leon-red/St1x/Software/Core/Inc/main.h

#define INT1_Pin GPIO_PIN_0
#define INT1_GPIO_Port GPIOA
#define INT1_EXTI_IRQn EXTI0_IRQn
#define TEMP_CON1_Pin GPIO_PIN_1
#define TEMP_CON1_GPIO_Port GPIOA
#define USB_VOLT_DET_Pin GPIO_PIN_2
#define USB_VOLT_DET_GPIO_Port GPIOA
#define KEY_DOWN_Pin GPIO_PIN_5
#define KEY_DOWN_GPIO_Port GPIOA
#define KEY_DOWN_EXTI_IRQn EXTI9_5_IRQn
#define KEY_MODE_Pin GPIO_PIN_6
#define KEY_MODE_GPIO_Port GPIOA
#define KEY_MODE_EXTI_IRQn EXTI9_5_IRQn
#define KEY_UP_Pin GPIO_PIN_7
#define KEY_UP_GPIO_Port GPIOA
#define KEY_UP_EXTI_IRQn EXTI9_5_IRQn
#define Buzzer_Pin GPIO_PIN_0
#define Buzzer_GPIO_Port GPIOB
#define OLED_IM_Pin GPIO_PIN_10
#define OLED_IM_GPIO_Port GPIOB
#define G_CS_Pin GPIO_PIN_11
#define G_CS_GPIO_Port GPIOB
#define OLED_CS_Pin GPIO_PIN_12
#define OLED_CS_GPIO_Port GPIOB
#define SPI2_SCK_Pin GPIO_PIN_13
#define SPI2_SCK_GPIO_Port GPIOB
#define SPI2_MISO_Pin GPIO_PIN_14
#define SPI2_MISO_GPIO_Port GPIOB
#define SPI2_MOSI_Pin GPIO_PIN_15
#define SPI2_MOSI_GPIO_Port GPIOB
#define OLED_DC_Pin GPIO_PIN_8
#define OLED_DC_GPIO_Port GPIOA
#define OLED_PW_EN_Pin GPIO_PIN_15
#define OLED_PW_EN_GPIO_Port GPIOA
#define OLED_Reset_Pin GPIO_PIN_3
#define OLED_Reset_GPIO_Port GPIOB
#define LED_BLUE_Pin GPIO_PIN_4
#define LED_BLUE_GPIO_Port GPIOB
#define LED_RGB_Pin GPIO_PIN_5
#define LED_RGB_GPIO_Port GPIOB
#define LED_GREEN_Pin GPIO_PIN_8
#define LED_GREEN_GPIO_Port GPIOB
#define LED_RED_Pin GPIO_PIN_9
#define LED_RED_GPIO_Port GPIOB
