leon-red/St1x/Software/St1xDrivers/St1xStatic.c

#include "St1xStatic.h"
#include "lis2dw12_reg.h"
#include "main.h"
#include "spi.h"
#include "St1xADC.h"
#include "St1xKey.h"
#include "St1xPID.h"
#include "St1xFlash.h"
#include "u8g2.h"
#include <stdio.h>
#include <string.h>
#include <math.h>

// 传感器相关变量
static stmdev_ctx_t dev_ctx;
static int16_t data_raw_acceleration[3];
static float acceleration_mg[3];
static uint8_t whoamI;
static uint8_t sensor_initialized = 0;
static float last_acceleration_mg[3] = {0.0f, 0.0f, 0.0f};  // 用于静置检测的上一帧数据
static float acceleration_change[3] = {0.0f, 0.0f, 0.0f};
static float zero_calibration_offset[3] = {0.0f, 0.0f, 0.0f};  // 归零校准的基准值
static uint8_t zero_calibration_saved = 0;  // 标记是否已保存归零校准数据到FLASH

// 静置时间控制参数（可配置，单位：分钟）
#define DEFAULT_STANDBY_TIME_REDUCE_TEMP 15    // 15分钟后进入休眠状态
#define DEFAULT_STANDBY_TIME_TURN_OFF 30       // 30分钟停止加热
#define DEFAULT_REDUCED_TEMPERATURE 160.0f    // 休眠状态下的温度维持

// 时间单位转换宏
#define MINUTES_TO_MILLISECONDS(minutes) ((minutes) * 60 * 1000)

// 静置时间控制变量
static uint32_t last_movement_time = 0;
static uint32_t standby_start_time = 0;
static uint8_t is_in_standby_mode = 0;
static uint8_t is_in_sleep_mode = 0;
static float original_target_temperature = 0.0f;
static uint8_t standby_mode_initialized = 0;
static uint8_t manually_stopped = 0;

// OLED屏幕亮度控制相关变量
static uint8_t oled_brightness = 255;
static uint8_t oled_standby_brightness = 76;
static u8g2_t* global_u8g2 = NULL;

// 传感器误差阈值，用于过滤小幅度的数值跳变
#define MOVEMENT_THRESHOLD 50.0f                      // 运动检测阈值 (mg)
#define STANDBY_TIME_THRESHOLD 5000                   // 静置时间阈值 (ms)

// 静置时间控制参数（可配置，单位：毫秒）
static uint32_t standby_time_reduce_temp = MINUTES_TO_MILLISECONDS(DEFAULT_STANDBY_TIME_REDUCE_TEMP);
static uint32_t standby_time_turn_off = MINUTES_TO_MILLISECONDS(DEFAULT_STANDBY_TIME_TURN_OFF);
static float reduced_temperature = DEFAULT_REDUCED_TEMPERATURE;

// SPI读写函数声明
static int32_t platform_write(void *handle, uint8_t reg, const uint8_t *bufp, uint16_t len);
static int32_t platform_read(void *handle, uint8_t reg, uint8_t *bufp, uint16_t len);
static void platform_delay(uint32_t ms);

/**
 * @brief 设置静置时间控制参数（单位：分钟）
 * @param time_to_reduce_temp 静置多长时间后开始降低温度（分钟）
 * @param time_to_turn_off    静置多长时间后停止加热（分钟）
 * @param reduced_temp        降低后的温度值
 */
void St1xStatic_SetStandbyParameters(uint32_t time_to_reduce_temp, uint32_t time_to_turn_off, float reduced_temp) {
    standby_time_reduce_temp = MINUTES_TO_MILLISECONDS(time_to_reduce_temp);
    standby_time_turn_off = MINUTES_TO_MILLISECONDS(time_to_turn_off);
    reduced_temperature = reduced_temp;
    
    if (reduced_temperature < 50.0f) reduced_temperature = 50.0f;
    if (reduced_temperature > max_temperature_limit) reduced_temperature = max_temperature_limit;
    
    if (standby_time_reduce_temp > standby_time_turn_off) {
        standby_time_reduce_temp = standby_time_turn_off;
    }
}

/**
 * @brief 使用默认宏定义参数设置静置时间控制
 */
void St1xStatic_SetDefaultStandbyParameters(void) {
    St1xStatic_SetStandbyParameters(DEFAULT_STANDBY_TIME_REDUCE_TEMP, DEFAULT_STANDBY_TIME_TURN_OFF, DEFAULT_REDUCED_TEMPERATURE);
}

/**
 * @brief 检查是否处于静置状态并控制温度
 */
static void St1xStatic_CheckStandbyControl(void) {
    if (!sensor_initialized) return;
    
    uint32_t current_time = HAL_GetTick();
    uint8_t reg;
    
    // 检查是否有新数据
    lis2dw12_flag_data_ready_get(&dev_ctx, &reg);
    
    // 读取加速度数据
    memset(data_raw_acceleration, 0x00, 3 * sizeof(int16_t));
    lis2dw12_acceleration_raw_get(&dev_ctx, data_raw_acceleration);
    
    // 转换为mg单位
    acceleration_mg[0] = lis2dw12_from_fs2_to_mg(data_raw_acceleration[0]);
    acceleration_mg[1] = lis2dw12_from_fs2_to_mg(data_raw_acceleration[1]);
    acceleration_mg[2] = lis2dw12_from_fs2_to_mg(data_raw_acceleration[2]);
    
    // 计算各轴加速度变化量
    acceleration_change[0] = fabsf(acceleration_mg[0] - last_acceleration_mg[0]);
    acceleration_change[1] = fabsf(acceleration_mg[1] - last_acceleration_mg[1]);
    acceleration_change[2] = fabsf(acceleration_mg[2] - last_acceleration_mg[2]);
    
    // 保存当前加速度值
    last_acceleration_mg[0] = acceleration_mg[0];
    last_acceleration_mg[1] = acceleration_mg[1];
    last_acceleration_mg[2] = acceleration_mg[2];
    
    // 计算总加速度变化量
    float total_accel_change = acceleration_change[0] + acceleration_change[1] + acceleration_change[2];

    // 检测到运动
    if (total_accel_change > MOVEMENT_THRESHOLD) {
        last_movement_time = current_time;
        standby_start_time = current_time;
        
        // 退出静置模式
        if (is_in_standby_mode || is_in_sleep_mode) {
            // 恢复屏幕供电（PA15）
            HAL_GPIO_WritePin(OLED_PW_EN_GPIO_Port, OLED_PW_EN_Pin, GPIO_PIN_SET);
            
            is_in_standby_mode = 0;
            is_in_sleep_mode = 0;
            if (!heating_status && !manually_stopped) {
                heating_status = 1;
                startHeatingControlTimer();
                setT12Temperature(original_target_temperature);
            } else if (heating_status) {
                setT12Temperature(original_target_temperature);
            }
        }
        // 设备被拿起后恢复加热
        else if (!heating_status && !manually_stopped && (is_in_standby_mode || is_in_sleep_mode)) {
            heating_status = 1;
            startHeatingControlTimer();
            setT12Temperature(original_target_temperature);
            manually_stopped = 0;
        }
        return;
    }
    
    // 只有在加热状态下才进行静置检测
    if (!heating_status) {
        standby_mode_initialized = 0;
        return;
    }
    
    // 初始化静置模式
    if (!standby_mode_initialized) {
        last_movement_time = current_time;
        standby_start_time = current_time;
        standby_mode_initialized = 1;
        manually_stopped = 0;
        return;
    }
    
    // 检查静置状态
    uint32_t time_since_last_movement = current_time - last_movement_time;
    uint32_t standby_duration = current_time - standby_start_time;
    
    if (time_since_last_movement >= STANDBY_TIME_THRESHOLD) {
        // 进入睡眠模式（停止加热）
        if (standby_duration >= standby_time_turn_off) {
            if (heating_status) {
                __HAL_TIM_SetCompare(&htim2, TIM_CHANNEL_2, 0);
                stopHeatingControlTimer();
                heating_status = 0;
                is_in_sleep_mode = 1;
                is_in_standby_mode = 0;
                manually_stopped = 0;
                
                // 关闭屏幕供电（PA15）
                HAL_GPIO_WritePin(OLED_PW_EN_GPIO_Port, OLED_PW_EN_Pin, GPIO_PIN_RESET);
            }
        }
        // 进入待机模式（降低温度）
        else if (standby_duration >= standby_time_reduce_temp) {
            if (!is_in_standby_mode && !is_in_sleep_mode) {
                original_target_temperature = target_temperature;
                is_in_standby_mode = 1;
                is_in_sleep_mode = 0;
            }
            
            // 设置降低后的温度
            if (heating_status && target_temperature != reduced_temperature) {
                setT12Temperature(reduced_temperature);
            }
        }
    }
}

// 传感器归零校准函数（基于当前位置）
static void St1xStatic_ZeroCalibration(void) {
    if (!sensor_initialized) return;
    
    // 等待传感器稳定
    platform_delay(100);
    
    // 读取多组数据进行平均，提高校准精度
    int32_t sum_x = 0, sum_y = 0, sum_z = 0;
    uint8_t calibration_samples = 10;
    
    for (uint8_t i = 0; i < calibration_samples; i++) {
        int16_t temp_data[3];
        
        // 等待新数据
        uint8_t reg;
        do {
            lis2dw12_flag_data_ready_get(&dev_ctx, &reg);
        } while (!reg);
        
        // 读取加速度数据
        lis2dw12_acceleration_raw_get(&dev_ctx, temp_data);
        
        sum_x += temp_data[0];
        sum_y += temp_data[1];
        sum_z += temp_data[2];
        
        platform_delay(10); // 10ms间隔
    }
    
    // 计算平均值作为当前位置的基准值
    int16_t current_offset_x = sum_x / calibration_samples;
    int16_t current_offset_y = sum_y / calibration_samples;
    int16_t current_offset_z = sum_z / calibration_samples;
    
    // 计算当前重力向量的大小（用于检测设备放置姿态）
    float current_gravity_mg = sqrtf(
        lis2dw12_from_fs2_to_mg(current_offset_x) * lis2dw12_from_fs2_to_mg(current_offset_x) +
        lis2dw12_from_fs2_to_mg(current_offset_y) * lis2dw12_from_fs2_to_mg(current_offset_y) +
        lis2dw12_from_fs2_to_mg(current_offset_z) * lis2dw12_from_fs2_to_mg(current_offset_z)
    );
    
    // 智能归零策略：基于当前位置进行归零
    // 无论设备处于什么姿态，都基于当前位置进行归零
    
    // 设置归零校准的基准值（保存到专门的数组中）
    zero_calibration_offset[0] = lis2dw12_from_fs2_to_mg(current_offset_x);
    zero_calibration_offset[1] = lis2dw12_from_fs2_to_mg(current_offset_y);
    zero_calibration_offset[2] = lis2dw12_from_fs2_to_mg(current_offset_z);
    
    // 保存归零校准数据到FLASH
    if (St1xFlash_SaveCalibrationData(zero_calibration_offset, 3)) {
        zero_calibration_saved = 1;
    }
    
    // 可以在这里添加硬件偏移校准（如果需要）
    // lis2dw12_offset_set(&dev_ctx, current_offset_x, current_offset_y, current_offset_z);
    
    // 保存校准状态用于调试
    static float last_calibration_gravity = 0.0f;
    last_calibration_gravity = current_gravity_mg;
}

// 初始化静态传感器显示模块
void St1xStatic_Init(void) {
    if (sensor_initialized) return;
    
    // 初始化传感器驱动接口
    dev_ctx.write_reg = platform_write;
    dev_ctx.read_reg = platform_read;
    dev_ctx.mdelay = platform_delay;
    dev_ctx.handle = &hspi2;
    
    platform_delay(20);
    
    // 检查设备ID
    lis2dw12_device_id_get(&dev_ctx, &whoamI);
    
    if (whoamI == LIS2DW12_ID) {
        uint8_t rst;
        lis2dw12_reset_set(&dev_ctx, PROPERTY_ENABLE);
        
        do {
            lis2dw12_reset_get(&dev_ctx, &rst);
        } while (rst);
        
        // 配置传感器
        lis2dw12_block_data_update_set(&dev_ctx, PROPERTY_ENABLE);
        lis2dw12_full_scale_set(&dev_ctx, LIS2DW12_2g);
        lis2dw12_filter_path_set(&dev_ctx, LIS2DW12_LPF_ON_OUT);
        lis2dw12_filter_bandwidth_set(&dev_ctx, LIS2DW12_ODR_DIV_4);
        lis2dw12_power_mode_set(&dev_ctx, LIS2DW12_HIGH_PERFORMANCE);
        lis2dw12_data_rate_set(&dev_ctx, LIS2DW12_XL_ODR_25Hz);
        
        sensor_initialized = 1;
        standby_mode_initialized = 0;
        
        // 尝试从FLASH加载归零校准数据
        if (St1xFlash_LoadCalibrationData(zero_calibration_offset, 3)) {
            zero_calibration_saved = 1;
        } else {
            // 如果FLASH中没有有效数据，执行归零校准
            St1xStatic_ZeroCalibration();
        }
    }
}

// 菜单项动作函数
void St1xStatic_Action(void) {
    St1xStatic_Init();
}

// 传感器数据显示函数
void St1xStatic_DisplayData(u8g2_t* u8g2) {
    // 检查静置控制
    St1xStatic_CheckStandbyControl();
    
    // 调用屏幕和LED控制函数
    St1xStatic_StandbyDisplayControl(u8g2);
    
    // 如果传入NULL，只执行检查逻辑，不进行显示
    if (u8g2 == NULL) {
        return;
    }
    
    uint8_t reg;
    
    // 读取数据前先检查传感器是否已初始化
    if (!sensor_initialized) {
        u8g2_ClearBuffer(u8g2);
        u8g2_SetFont(u8g2, u8g2_font_ncenB08_tr);
        u8g2_DrawStr(u8g2, 0, 20, "Sensor Not Found!");
        u8g2_SendBuffer(u8g2);
        return;
    }
    
    // 检查是否有新数据
    lis2dw12_flag_data_ready_get(&dev_ctx, &reg);
    
    if (reg) {
        // 读取加速度数据
        memset(data_raw_acceleration, 0x00, 3 * sizeof(int16_t));
        lis2dw12_acceleration_raw_get(&dev_ctx, data_raw_acceleration);
        
        // 转换为mg单位
        acceleration_mg[0] = lis2dw12_from_fs2_to_mg(data_raw_acceleration[0]);
        acceleration_mg[1] = lis2dw12_from_fs2_to_mg(data_raw_acceleration[1]);
        acceleration_mg[2] = lis2dw12_from_fs2_to_mg(data_raw_acceleration[2]);
    }
    
    // 显示数据
    u8g2_ClearBuffer(u8g2);
    
    // 显示标题
    u8g2_SetFont(u8g2, u8g2_font_ncenB08_tr);
    u8g2_DrawStr(u8g2, 0, 10, "6-Axis Sensor Data");
    
    // 显示X轴数据（相对于归零校准基准值的差值）
    u8g2_SetFont(u8g2, u8g2_font_spleen6x12_mf);
    char x_str[20];
    sprintf(x_str, "X: %6.2f mg", acceleration_mg[0] - zero_calibration_offset[0]);
    u8g2_DrawStr(u8g2, 0, 25, x_str);
    
    // 显示Y轴数据（相对于归零校准基准值的差值）
    char y_str[20];
    sprintf(y_str, "Y: %6.2f mg", acceleration_mg[1] - zero_calibration_offset[1]);
    u8g2_DrawStr(u8g2, 0, 37, y_str);
    
    // 显示Z轴数据（相对于归零校准基准值的差值）
    char z_str[20];
    sprintf(z_str, "Z: %6.2f mg", acceleration_mg[2] - zero_calibration_offset[2]);
    u8g2_DrawStr(u8g2, 0, 49, z_str);
    
    // 显示设备ID
    char id_str[20];
    sprintf(id_str, "ID: 0x%02X", whoamI);
    u8g2_DrawStr(u8g2, 0, 61, id_str);

    u8g2_DrawStr(u8g2, 0, 71, "Press MODE to 6-Axis");
    u8g2_DrawStr(u8g2, 0, 80, "Sensor Calibration");

    
    u8g2_SendBuffer(u8g2);
}

// SPI读写函数
static int32_t platform_write(void *handle, uint8_t reg, const uint8_t *bufp, uint16_t len) {
    HAL_GPIO_WritePin(G_CS_GPIO_Port, G_CS_Pin, GPIO_PIN_RESET);
    HAL_SPI_Transmit(handle, &reg, 1, 1000);
    HAL_SPI_Transmit(handle, (uint8_t *) bufp, len, 1000);
    HAL_GPIO_WritePin(G_CS_GPIO_Port, G_CS_Pin, GPIO_PIN_SET);
    return 0;
}

static int32_t platform_read(void *handle, uint8_t reg, uint8_t *bufp, uint16_t len) {
    reg |= 0x80;
    HAL_GPIO_WritePin(G_CS_GPIO_Port, G_CS_Pin, GPIO_PIN_RESET);
    HAL_SPI_Transmit(handle, &reg, 1, 1000);
    HAL_SPI_Receive(handle, bufp, len, 1000);
    HAL_GPIO_WritePin(G_CS_GPIO_Port, G_CS_Pin, GPIO_PIN_SET);
    return 0;
}

static void platform_delay(uint32_t ms) {
    HAL_Delay(ms);
}

// 显示调试信息
void St1xStatic_DisplayDebugInfo(u8g2_t* u8g2) {
    u8g2_SetFont(u8g2, u8g2_font_spleen6x12_mf);
    
    // 只有在加热状态下才显示时间信息
    uint32_t time_since_last_movement = 0;
    
    if (heating_status) {
        time_since_last_movement = HAL_GetTick() - last_movement_time;
    }
    
    // 直接使用加速度变化量之和
    float total_accel = acceleration_change[0] + acceleration_change[1] + acceleration_change[2];
    uint8_t in_standby = St1xStatic_IsInStandbyMode();
    
    // 计算当前重力向量大小（用于校准状态显示）
    float current_gravity = sqrtf(
        last_acceleration_mg[0] * last_acceleration_mg[0] +
        last_acceleration_mg[1] * last_acceleration_mg[1] +
        last_acceleration_mg[2] * last_acceleration_mg[2]
    );
    
    // 格式化并显示信息
    char debug_str1[30];
    char debug_str2[30];
    char debug_str3[30];
    
    sprintf(debug_str1, "A:%.0f SB:%d HT:%d", total_accel, in_standby, heating_status);
    sprintf(debug_str2, "L:%lu G:%.0f", time_since_last_movement/1000, current_gravity);
    sprintf(debug_str3, "Z:%.0f", last_acceleration_mg[2]);
    
    // 在指定位置显示
    u8g2_DrawStr(u8g2, 15, 26, debug_str1);
    u8g2_DrawStr(u8g2, 15, 38, debug_str2);
    u8g2_DrawStr(u8g2, 15, 50, debug_str3);
    
    // 添加MODE按键校准提示
    u8g2_DrawStr(u8g2, 15, 62, "MODE:Zero Calib");
}

// 获取当前静置持续时间
uint32_t St1xStatic_GetStandbyDuration(void) {
    if (!standby_mode_initialized || !heating_status) {
        return 0;
    }
    return HAL_GetTick() - standby_start_time;
}

// 检查是否处于待机模式
uint8_t St1xStatic_IsInStandbyMode(void) {
    if (!heating_status) {
        return 0;
    }
    return is_in_standby_mode;
}

// 检查是否处于睡眠模式
uint8_t St1xStatic_IsInSleepMode(void) {
    return is_in_sleep_mode;
}

// 设置手动停止标记
void St1xStatic_SetManuallyStopped(uint8_t stopped) {
    manually_stopped = stopped;
}

// 检查是否手动停止加热
uint8_t St1xStatic_IsManuallyStopped(void) {
    return manually_stopped;
}

// 手动归零校准函数（可在菜单中调用）
void St1xStatic_ManualZeroCalibration(void) {
    if (!sensor_initialized) {
        // 如果传感器未初始化，先初始化
        St1xStatic_Init();
    } else {
        // 执行归零校准
        St1xStatic_ZeroCalibration();
    }
}

// OLED屏幕亮度控制函数
static void OLED_SetBrightness(u8g2_t* u8g2, uint8_t brightness) {
    if (u8g2 != NULL) {
        u8x8_SetContrast(u8g2_GetU8x8(u8g2), brightness);
    }
}

// 静置状态下的屏幕亮度控制
void St1xStatic_StandbyDisplayControl(u8g2_t* u8g2) {
    // 检查是否处于传感器数据显示界面
    extern uint8_t is_static_display_mode(void);
    if (is_static_display_mode()) {
        // 在传感器数据显示界面，保持正常亮度
        if (u8g2 != NULL) {
            OLED_SetBrightness(u8g2, oled_brightness);
        }
        return;
    }
    
    // 检查当前静置状态
    uint32_t standby_duration = St1xStatic_GetStandbyDuration();
    uint8_t in_standby_mode = St1xStatic_IsInStandbyMode();
    
    // 统一调度逻辑
    if (!heating_status && !manually_stopped) {
        // 静置触发睡眠：停止加热且非手动停止，关闭屏幕
        if (u8g2 != NULL) {
            OLED_SetBrightness(u8g2, 0);
        }
    }
    else if (in_standby_mode && heating_status) {
        // 静置触发待机：降低温度但仍保持加热，设置屏幕亮度为30%
        if (u8g2 != NULL) {
            OLED_SetBrightness(u8g2, oled_standby_brightness);
        }
    }
    else {
        // 正常工作状态：恢复OLED屏幕正常亮度
        if (u8g2 != NULL) {
            OLED_SetBrightness(u8g2, oled_brightness);
        }
    }
}

// 设置全局u8g2对象指针
void St1xStatic_SetGlobalU8g2(u8g2_t* u8g2) {
    global_u8g2 = u8g2;
}

// 定时器回调函数
void St1xStatic_TimerCallback(void) {
    static uint32_t last_call_time = 0;
    uint32_t current_time = HAL_GetTick();
    
    // 每100ms执行一次控制
    if (current_time - last_call_time < 100) {
        return;
    }
    last_call_time = current_time;
    
    // 调用屏幕亮度控制函数
    St1xStatic_StandbyDisplayControl(global_u8g2);
}
