leon-red/St1x/Software/St1xDrivers/Inc/bmp.h

#ifndef __BMP_H
#define __BMP_H

unsigned char Logo[] =
{0x00,0x00,0x00,0x00,0x00,0x00,0x00,0x00,0x00,0x00,0x00,0x00,0x00,0x00,0x00,0x00,0x00,0x00,0x00,0x00,0x00,0x00,0x00,0x00,0x00,0x00,0x00,0x00,0x00,0x00,0x00,0x00,0x00,0x00,0x00,0x00,0x00,0x00,0x00,0x00,0x00,0x00,0x00,0x00,0x00,0x00,0x00,0x00,0x00,0x00,0x00,0x00,0x00,0x00,0x00,0x00,0x00,0x00,0x00,0x00,0x00,0x00,0x00,0x00,0x00,0x00,0x00,0x00,0x00,0x00,0x00,0x00,0x00,0x00,0x00,0x00,0x00,0x00,0x00,0x00,0xC0,0xC3,0xFF,0x00,0xF8,0x01,0x7C,0xC0,0x03,0xE0,0x7F,0xF0,0x7F,0x7C,0xC0,0x03,0xC0,0xC3,0xFF,0x03,0xFE,0x07,0x7C,0xC0,0x03,0xE0,0xFF,0xF0,0x7F,0x7C,0xC0,0x03,0xC0,0xC3,0xFF,0x03,0xFF,0x1F,0xFC,0xC0,0x03,0xE0,0xFF,0xF1,0x7F,0xFC,0xC0,0x03,
 0xC0,0xC3,0xC3,0x87,0x0F,0x1F,0xFC,0xC0,0x03,0xE0,0xE1,0xF3,0x00,0xFC,0xC0,0x03,0xC0,0xC3,0x83,0xC7,0x07,0x3C,0xFC,0xC1,0x03,0xE0,0xC1,0xF3,0x00,0xFC,0xC1,0x03,0xC0,0xC3,0x83,0xC7,0x03,0x3C,0xFC,0xC3,0x03,0xE0,0xC1,0xF3,0x00,0xFC,0xC3,0x03,0xC0,0xC3,0x83,0xE7,0x01,0x78,0xBC,0xC3,0x03,0xE0,0xC1,0xF3,0x00,0xBC,0xC3,0x03,0xC0,0xC3,0xC3,0xE3,0x01,0x78,0xBC,0xC7,0x03,0xE0,0xC1,0xF3,0x3F,0xBC,0xC7,0x03,0xC0,0xC3,0xFF,0xE1,0x01,0x78,0x3C,0xCF,0x03,0xE0,0xE1,0xF1,0x3F,0x3C,0xCF,0x03,0xC0,0xC3,0xFF,0xE0,0x01,0x78,0x3C,0xCE,0x03,0xE0,0xFF,0xF1,0x3F,0x3C,0xCE,0x03,0xC0,0xC3,0xFF,0xE0,0x01,0x78,0x3C,0xDE,0x03,0xE0,0xFF,0xF0,0x00,0x3C,0xDE,0x03,
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
0x00,0x00,0x00,0x00,0x00,0x00,0xFC,0xFF,0xE0,0xFF,0xFF,0x03,0x00,0x00,0x00,0x00,
0x00,0x00,0x00,0x00,0x00,0x00,0xF8,0xFF,0xE0,0xFF,0xFF,0x03,0x00,0x00,0x00,0x00,
0x00,0x00,0x00,0x00,0x00,0x00,0xF0,0xFF,0xC1,0xFF,0x7F,0x00,0x00,0x00,0x00,0x00,
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
};

#endif
